mchilcott/big_clock/src/HAL.h

#pragma once

// Button Pins
#define BTN_OPT      2
#define BTN_UP       4
#define BTN_DOWN     3

#define DISP_HEIGHT  4
#define DISP_WIDTH  20

#define LED_PIN      6

// RTC Address (I2C)
#define RTC_ADDR unk
